KatESaeed/3D-Protein-Folding-Tool/Nonpolar/isoleucine.stl

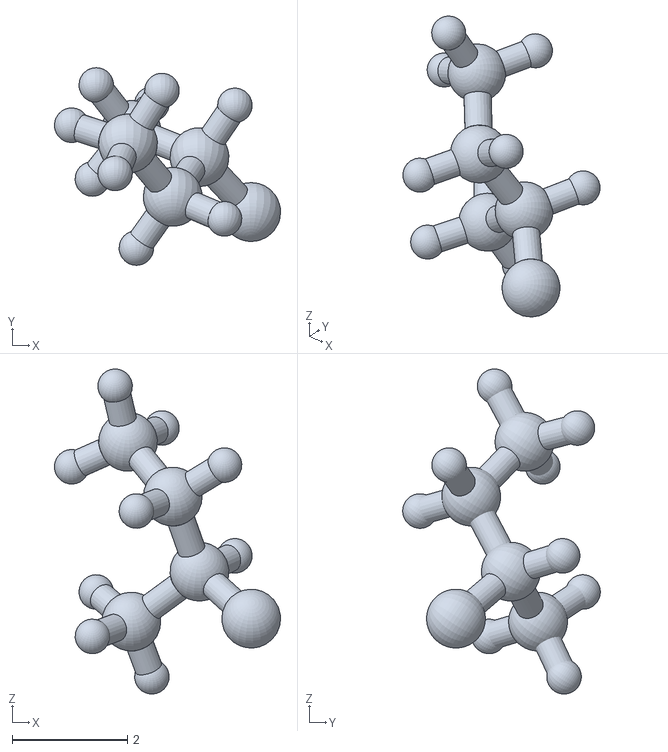
[picture p15: CAD file, 2026-04-23]
Nonpolar/isoleucine.stl
3.92 x 3.42 x 5.63
