KatESaeed/3D-Protein-Folding-Tool/Polar/serine.stl

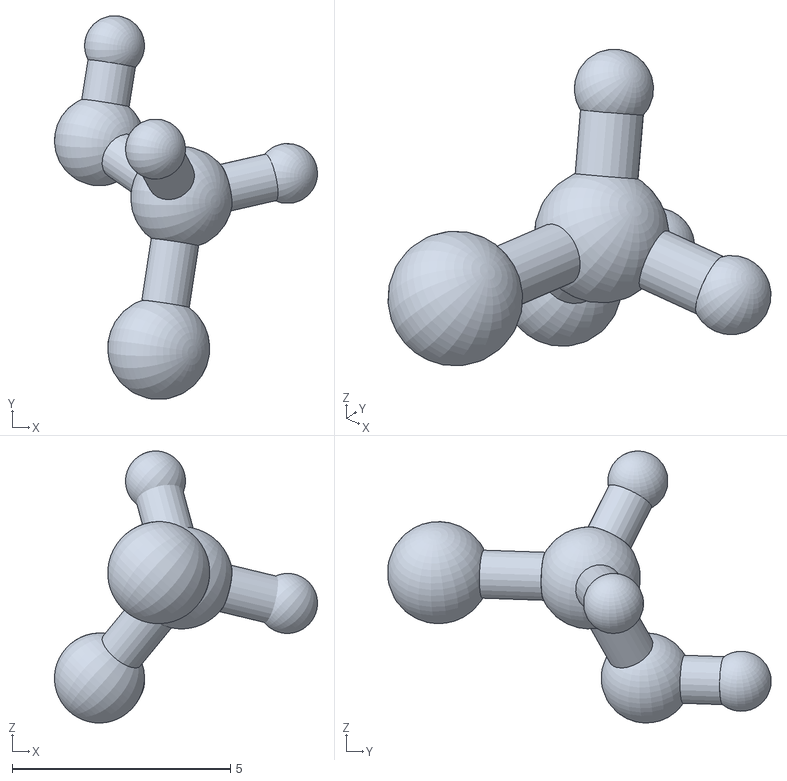
[picture p16: CAD file, 2026-04-23]
Polar/serine.stl
6.03 x 8.77 x 6.23
