KatESaeed/3D-Protein-Folding-Tool/Nonpolar/valine.stl

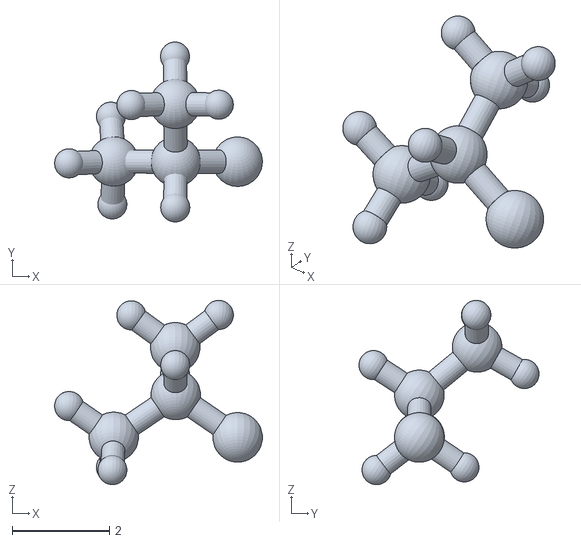
[picture p17: CAD file, 2026-04-23]
Nonpolar/valine.stl
4.27 x 3.70 x 3.78
