KatESaeed/3D-Protein-Folding-Tool/Polar/cysteine.stl

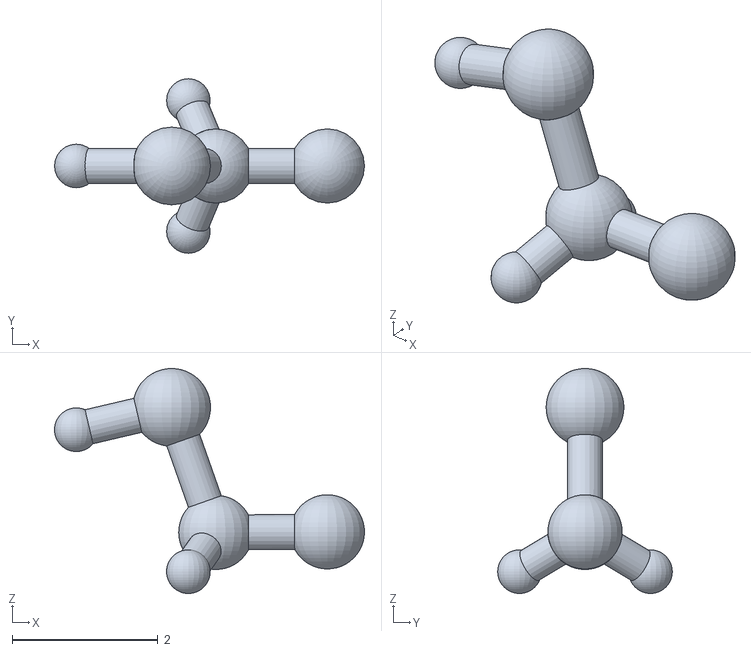
[picture p18: CAD file, 2026-03-13]
Polar/cysteine.stl
4.26 x 2.40 x 3.09
