KatESaeed/3D-Protein-Folding-Tool/Nonpolar/glycine.stl

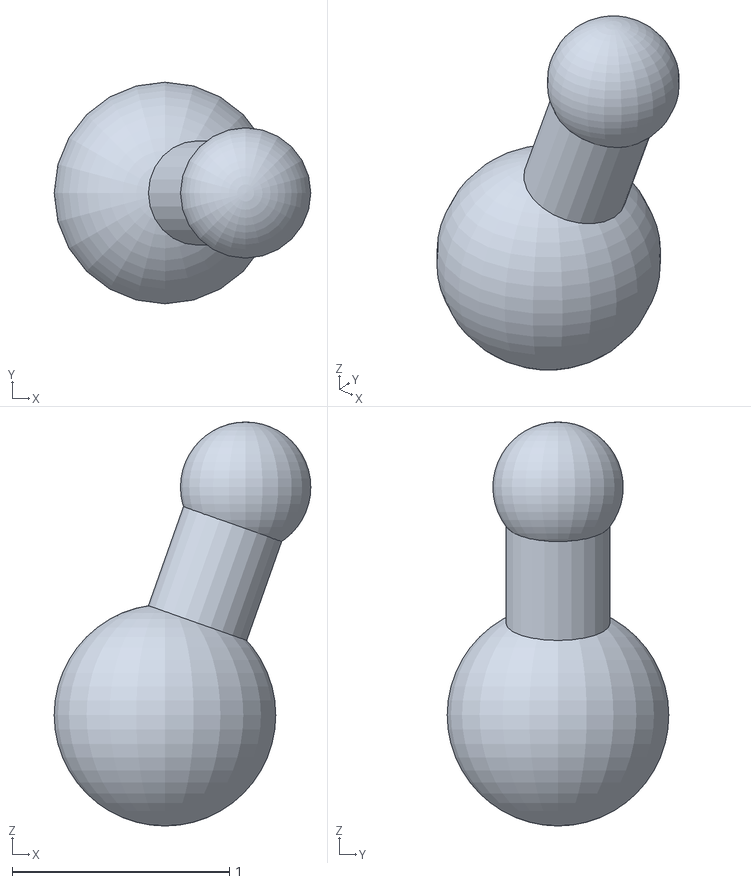
[picture p19: CAD file, 2026-04-23]
Nonpolar/glycine.stl
1.18 x 1.02 x 1.86
