KatESaeed/3D-Protein-Folding-Tool/Nonpolar/alanine.stl

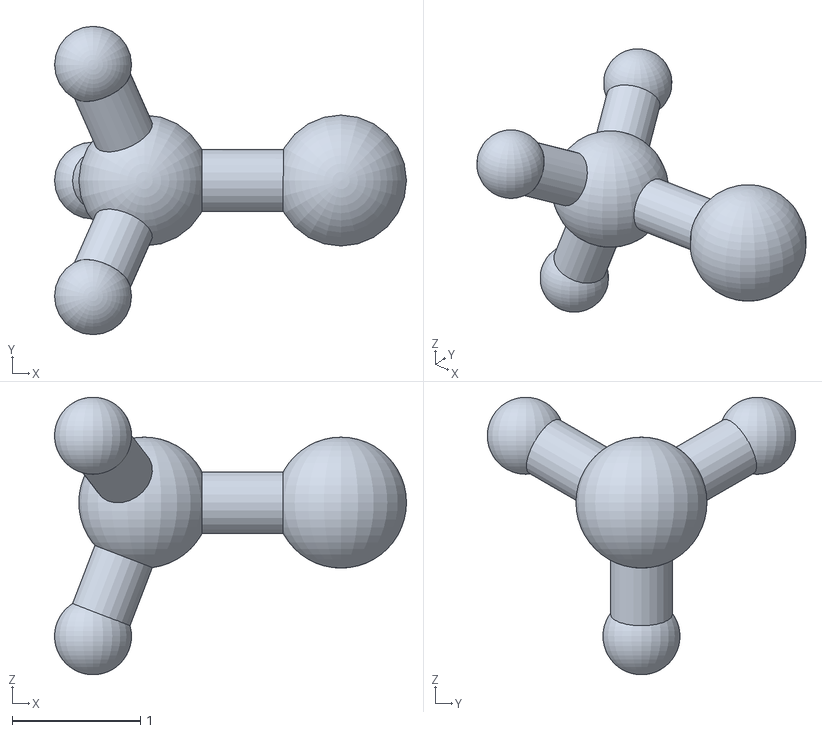
[picture p20: CAD file, 2026-04-23]
Nonpolar/alanine.stl
2.74 x 2.40 x 2.16
