KatESaeed/3D-Protein-Folding-Tool/Nonpolar/leucine.stl

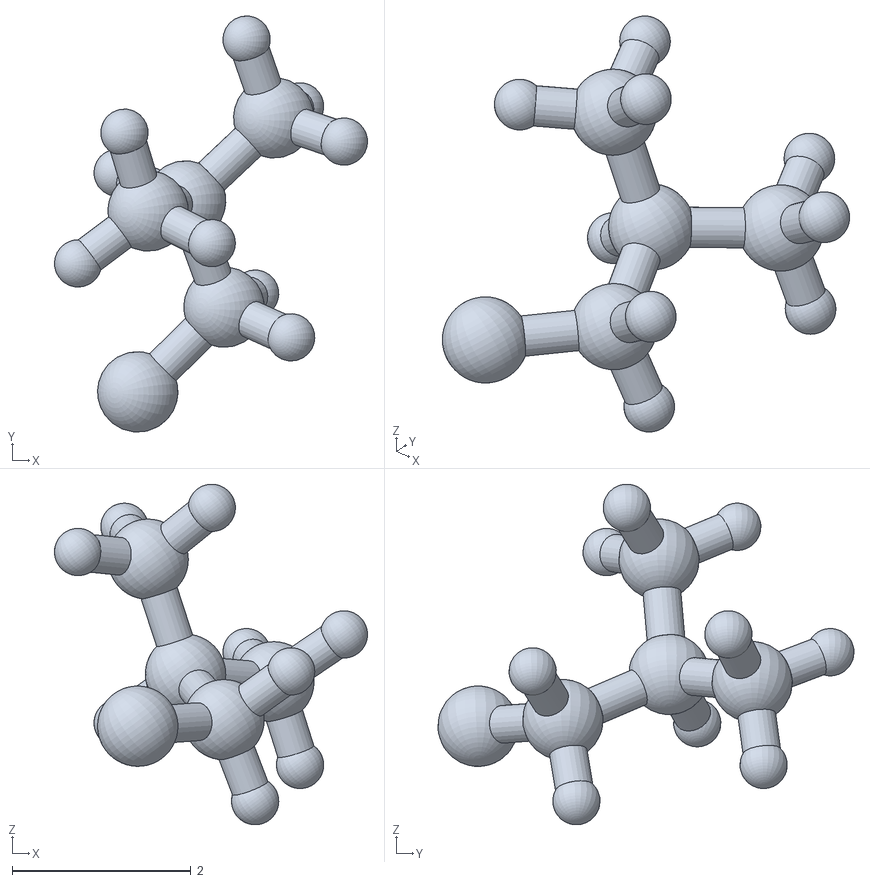
[picture p21: CAD file, 2026-04-23]
Nonpolar/leucine.stl
3.51 x 4.66 x 3.82
